EinShides/Nebula-Keypad/3d Component Models/D_SOD-123.step

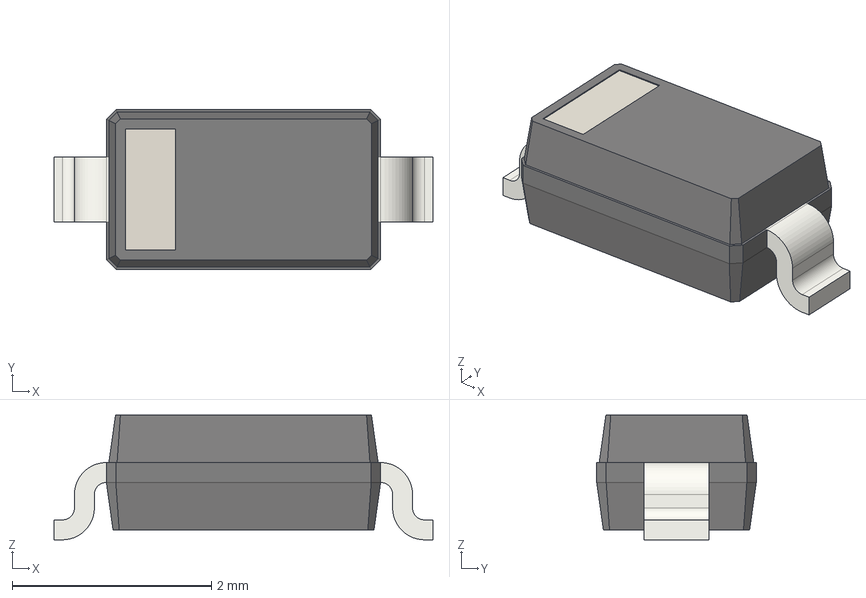
[picture p18: CAD file, 2021-08-11]
3d Component Models/D_SOD-123.step
3.80 x 1.60 x 1.25 mm
