EinShides/Nebula-Keypad/3d Component Models/R_0805_2012Metric.step

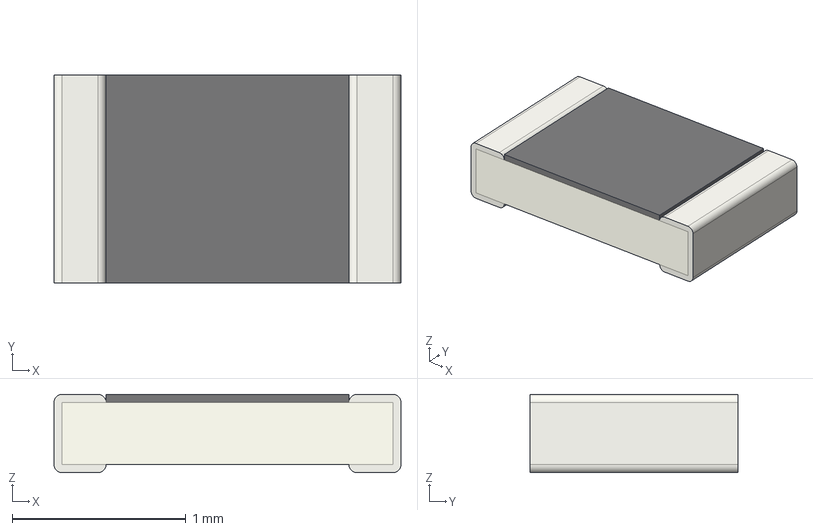
[picture p19: CAD file, 2021-08-11]
3d Component Models/R_0805_2012Metric.step
2.00 x 1.20 x 0.45 mm
